Ciosepp/Monophono-keyboard/Monophono/src/Functions.cpp

#include "Functions.h"

#include "config.h"
#include "hwFunct.h"
#include "mono.h"
#include "pin_config.h"
#include "arpeggiator.h"

void Init() {
    Serial.print("MONOPHONO V");
    Serial.print(version);
    Serial.println("");
    pinInit();
    Serial.println("pin INIT OK");
    dacInit();
    Serial.println("DAC INIT OK");
}

bool noteDown(int i, bool* noteScan, bool* noteTrans) {
    return noteScan[i] && noteTrans[i];
}
bool noteUp(int i, bool* noteScan, bool* noteTrans) {
    return noteScan[i] && !noteTrans[i];
}

void elabControls() {
    //ARP_MODE_RAW = map(ARP_MODE_RAW, 0, 1023, 0, 3);
    ARP_MODE_RAW = ARP_MODE_RAW /340;
    switch (ARP_MODE_RAW) {
        case 0:
            arpMode = UP;
            break;

        case 1:
            arpMode = UD;
            break;

        case 2:
            arpMode = DOWN;
            break;

        case 3:
            arpMode = RAND;
            break;

        default:
            break;
    }

    //ARP_STATE_RAW = map(ARP_STATE_RAW, 0, 1023, 0, 2);
    ARP_STATE_RAW = ARP_STATE_RAW/340;

    switch (ARP_STATE_RAW) {
        case 0:
            arpState = OFF;
            arpeggioState = AWAITING_KEYPRESS;
            break;

        case 1:
            arpState = HOLD;
            break;

        case 2:
            arpState = LATCH;
            break;

        default:
            break;
    }

    ARP_OCTAVE =ARP_OCTAVE_RAW/350;

    CK_AMT = map(CK_AMT, 0, 1023, 60, 300);
}

void logic() {
    elabControls();
    // switch between MONO, arpeggiator HOLD or LATCH
    switch(arpState){
        case OFF:
            mono();
            MONO_GATE();
        break;
        case HOLD:
            arpeggiatorHold();
        break;
        case LATCH:
            arpeggiatorLatch();
        break;
    } 

    // dev
    //mono();
}

void readInputs() {
    scanKeyboard();
    scanControls();
    scanClock();
}
